CodreanuDan/DistriburedSystems_MonitoringDevice_DsMd/HW/ICircuit/Motor_and_LED_Control .cir

$ 67 32 6.25E-05 0 5 50 Black 1376 1760 false

v 672 1056 672 992 0 0 1 5 0 0 0.5 
d 1088 1056 1088 960 1 0.805904783
g 672 1152 672 1248 0
v 928 1120 928 1056 0 2 1000 3.3 0 0 0.5 
t 928 960 928 896 1 1 0 0 1000
w 928 1152 928 1120 0
r 928 960 928 1056 0 220
w 1088 960 1088 896 0
w 960 896 1088 896 0
w 928 1152 1088 1152 0
w 1088 1056 1088 1152 0
w 928 1152 672 1152 0
w 672 1056 672 1152 0
w 1088 896 1248 896 0
w 1248 992 1248 896 0
w 1088 1152 1248 1152 0
w 1248 1152 1248 1056 0
w 672 992 672 896 0
w 896 896 672 896 3
247 1248 992 1248 1056 0 3 200 0.07 0.6 45 0.001 0.0001
v 672 1504 672 1440 0 0 1 3.3 0 0 0.5 
g 672 1600 672 1696 0
v 928 1568 928 1504 0 2 1000 3.3 0 0 0.5 
t 928 1408 928 1344 1 1 0 0 1000
w 928 1600 928 1568 0
r 928 1408 928 1504 0 220
w 928 1600 1248 1600 0
w 928 1600 672 1600 0
w 672 1504 672 1600 0
w 1248 1600 1248 1504 0
w 672 1440 672 1344 0
w 896 1344 672 1344 3
r 1024 1344 1152 1344 0 220
w 960 1344 1024 1344 0
w 1152 1344 1248 1344 0
w 1248 1440 1248 1344 0
181 1248 1440 1248 1504 0 0 0.001 3 0.04 0.04
o 0 0 0 0 1 1 0.0100000000202272 1 -5 5
